Fredobedo/JVS2X/images/IMG_8981.jpg

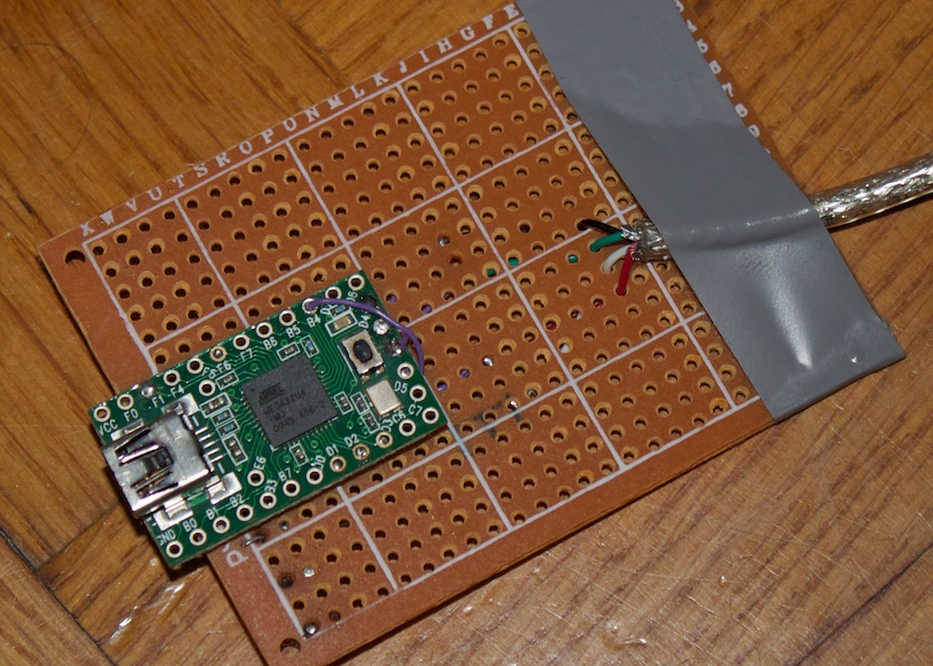
images/IMG_8981.jpg
