Fredobedo/JVS2X/images/IMG_8983.jpg

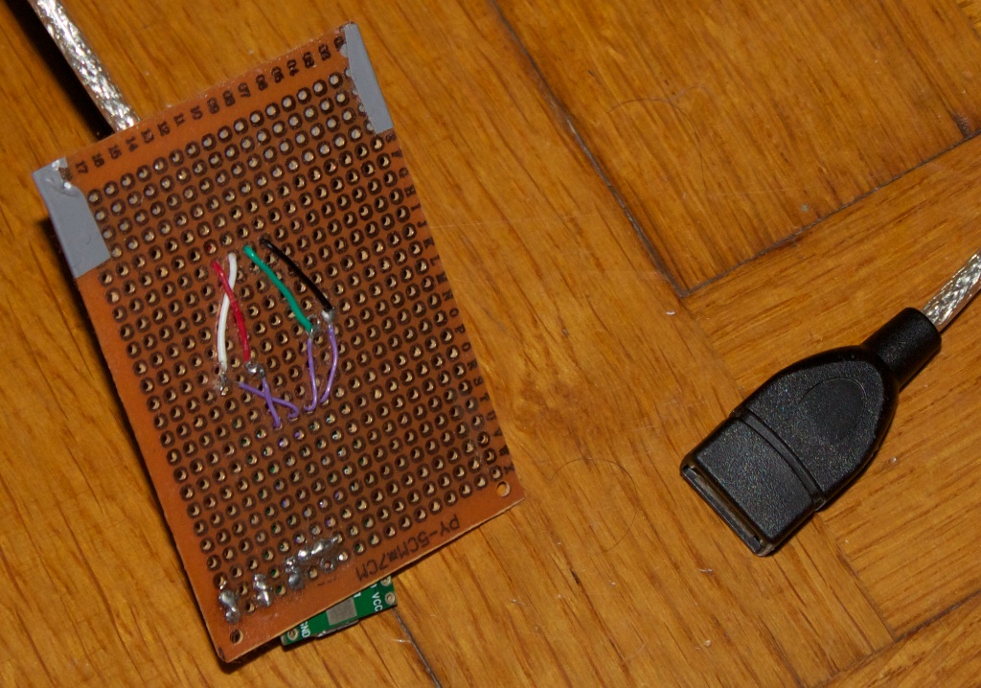
images/IMG_8983.jpg
