Fredobedo/JVS2X/images/IMG_8985.jpg

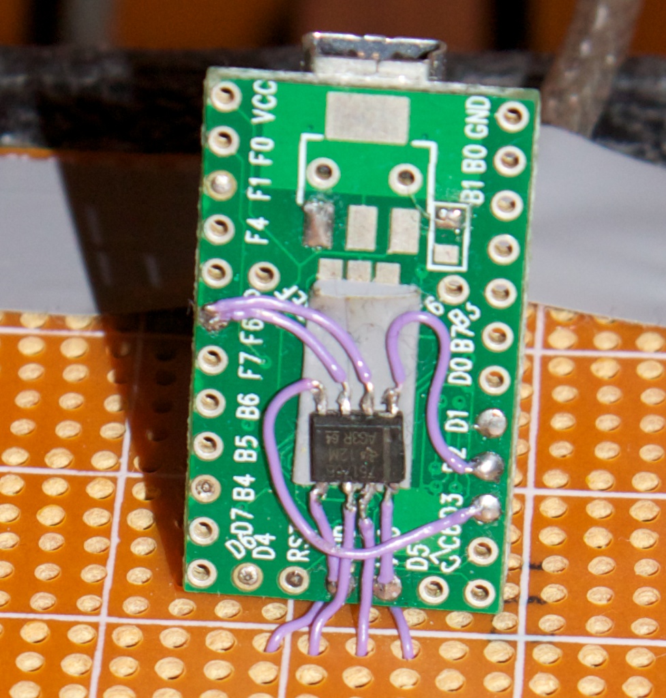
images/IMG_8985.jpg
