Fredobedo/JVS2X/images/teensy20_card2a_rev5.png

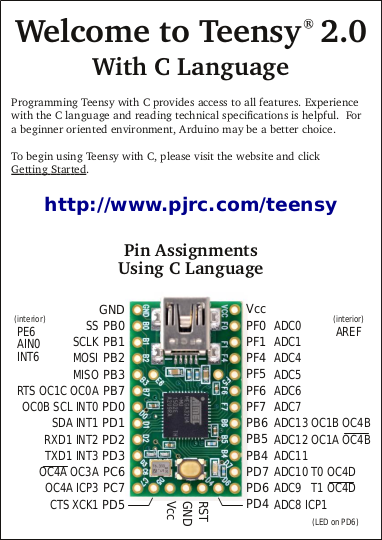
images/teensy20_card2a_rev5.png
