Fredobedo/JVS2X/images/x8s29ytc.jpg

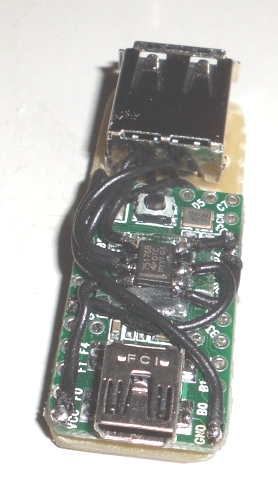
images/x8s29ytc.jpg
