Fredobedo/JVS2X/src/JVS_UART/jvs_uart.cpp

#include <Arduino.h>
#include "JVS_UART/jvs_uart.h"

JvsUart::JvsUart(HardwareSerial& serial):_Uart(serial) {}

int JvsUart::getByte()
{
    delayMicroseconds(SPECS_TIMING_MASTER_READ_TIMEOUT);
    return _Uart.read(); 
}


int JvsUart::buildRawRequestPacket(char destination, char data[], int size, char rawPacket[])
{
    TRACE(2, "Building Packet:");
    int cp=0;

    rawPacket[cp++]=SYNC;          TRACE(2, " E0");
    rawPacket[cp++]=destination;   TRACE_ARGS(2, " %02X", destination);
    /* The byte count is:
            the number of bytes left in the packet, 
            + the SUM byte.*/
    rawPacket[cp++]=size + 1;      TRACE_ARGS(2, " %02X", size + 1);
    char sum = destination + size + 1;

    /* Please note that MARK processing (adding escapes for SYNC char in payload) is transparent to the protocol                                        */
    /*  -> We don't have to take into account of the potential additional characters in the SIZE & SUM calculation                                      */
    /* In fact encoding processing is normally performed after processing the number of bytes and SUM, therefore it is not taken into account for SUM   */
    int i;
    for (i = 0; i < size; i++) {
        
        if (data[i] == SYNC || data[i] == ESCAPE) {
            rawPacket[cp++]=ESCAPE;                        TRACE_ARGS(2, " %02X", (uint8_t)ESCAPE);
            rawPacket[cp++]=data[i] - 1;                   TRACE_ARGS(2, " %02X", (uint8_t)(data[i] - 1));
        }
        else {
            rawPacket[cp++]=data[i];                       TRACE_ARGS(2, " %02X", (uint8_t)data[i]);
        }
        sum = (sum + data[i]) % 256;
    }
    rawPacket[cp++]=sum;                             TRACE_ARGS(2, " %02X", (uint8_t)(sum % 256));
    rawPacket[cp++]='\0';
    
    TRACE_ARGS_P(2, "\n -> build done, request length %d\n", i + 4);
    return i + 4;
}

bool JvsUart::writeRawPacket(const char data[], int size)
{
    for (int i = 0; i < size; i++)  _Uart.write(data[i]);
    
    _Uart.flush();
    return true;
}

/* Serial.write() sends binary data <> Serial.print() with sends the ASCII representation */
bool JvsUart::writePacket(char destination, char data[], int payloadSize) 
{

    if(strlen(data)>0)
    {
         TRACE(2, "Sending Packet:");

        _Uart.write(SYNC);              TRACE(2, " E0");
        _Uart.write(destination);       TRACE_ARGS(2, " %02X", (uint8_t)destination);
        /* The byte count is:
              payloadSize, 
              + the SUM byte.*/
        _Uart.write(payloadSize + 1);   TRACE_ARGS(2, " %02X", (uint8_t)destination);

        //SUM = (destination + size (payloadSize + sum Byte) + each payload byte value) % 256;
        char sum = destination + payloadSize + 1;

        /* Please note that MARK processing (adding escapes for SYNC char in payload) is transparent to the protocol     */
        /*  -> We don't have to take into account of the potential additional characters in the SIZE & SUM calculation   */
        for (int i = 0; i < payloadSize; i++) {
            if (data[i] == SYNC || data[i] == ESCAPE) {
                _Uart.write(ESCAPE);                        TRACE_ARGS(2, " %02X", (uint8_t)ESCAPE);
                _Uart.write(data[i] - 1);                   TRACE_ARGS(2, " %02X", (uint8_t)(data[i] - 1));
            }
            else {
                _Uart.write(data[i]);                       TRACE_ARGS(2, " %02X", (uint8_t)data[i]);
            }
            sum= (sum + data[i]) % 256;
        }

        _Uart.write(sum);                                   TRACE_ARGS(2, " %02X", (uint8_t)sum);
        _Uart.flush();
        TRACE(2, "\nPacket sent\n");

        return true;
    }
    return false;
}
